PerlPooch/MQTT-Agent/MQTT-Agent-Hardware/Gerbers/V1/MQTT Relay-F_Cu.pdf

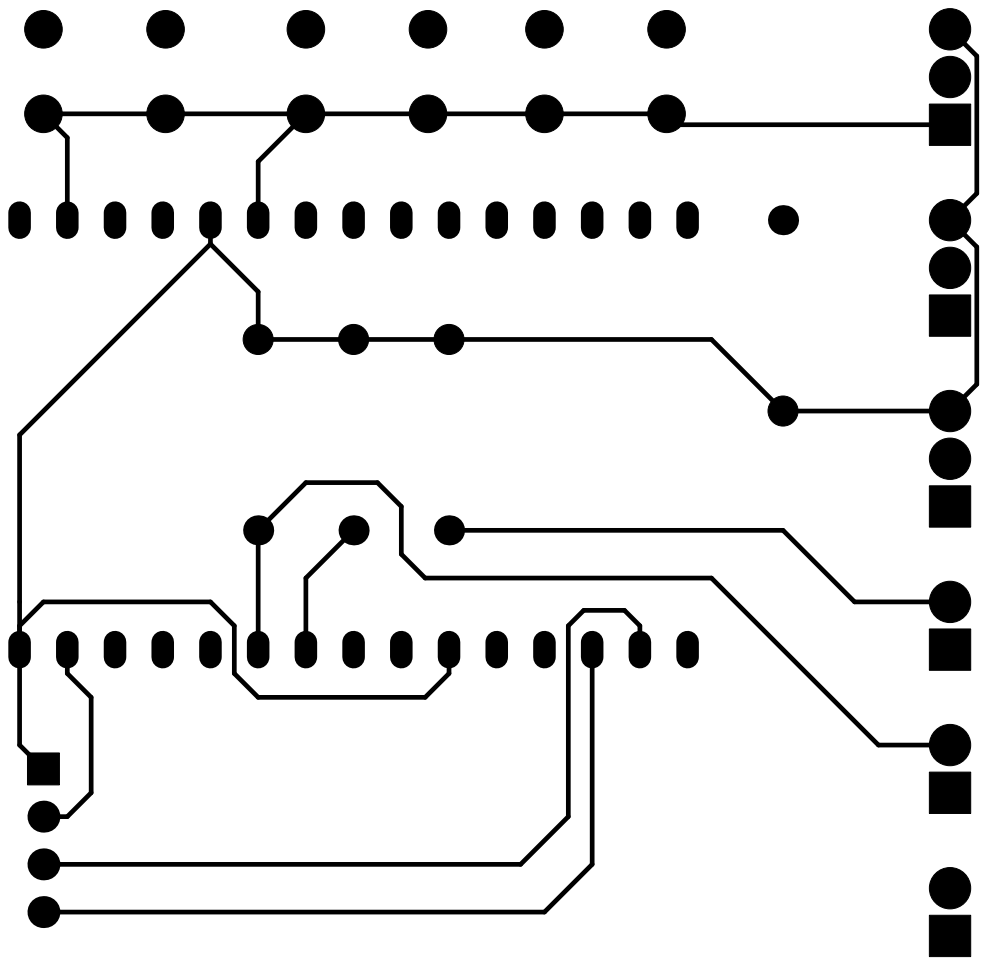
[picture p24: page 1]
