PerlPooch/MQTT-Agent/MQTT-Agent-Hardware/Gerbers/V1/MQTT Relay-F_SilkS.pdf

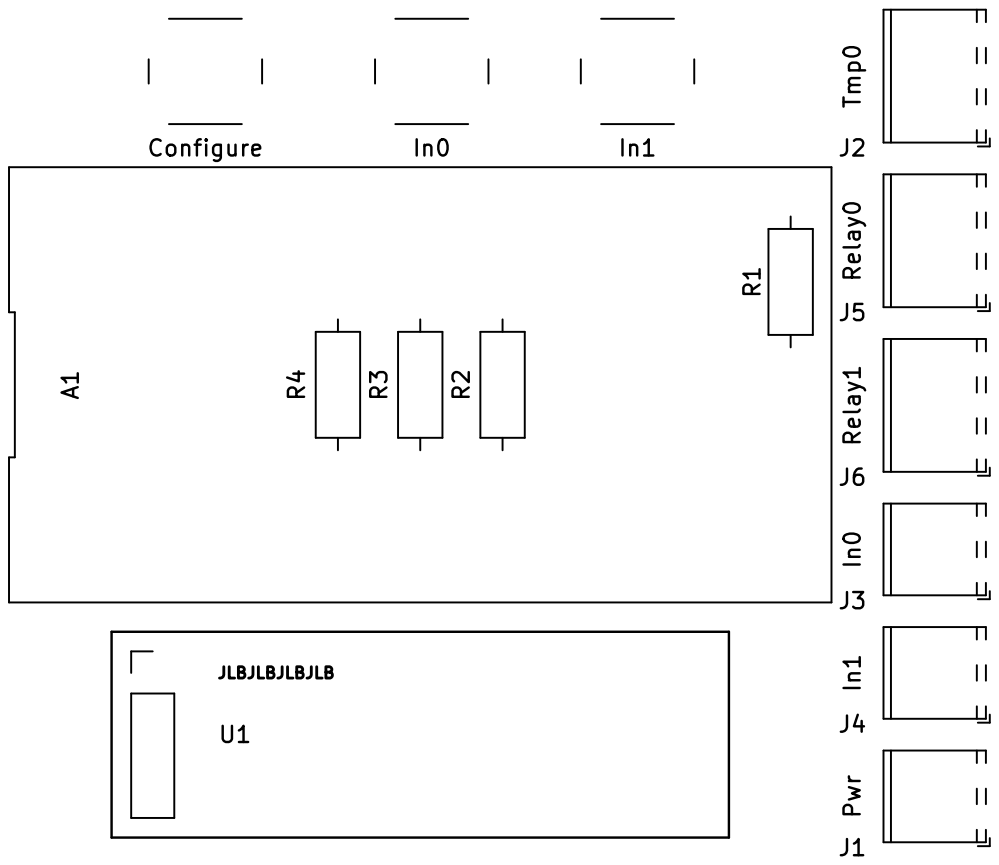
[picture p25: page 1]
