PerlPooch/MQTT-Agent/MQTT-Agent-Hardware/Gerbers/V1/MQTT Relay.pdf

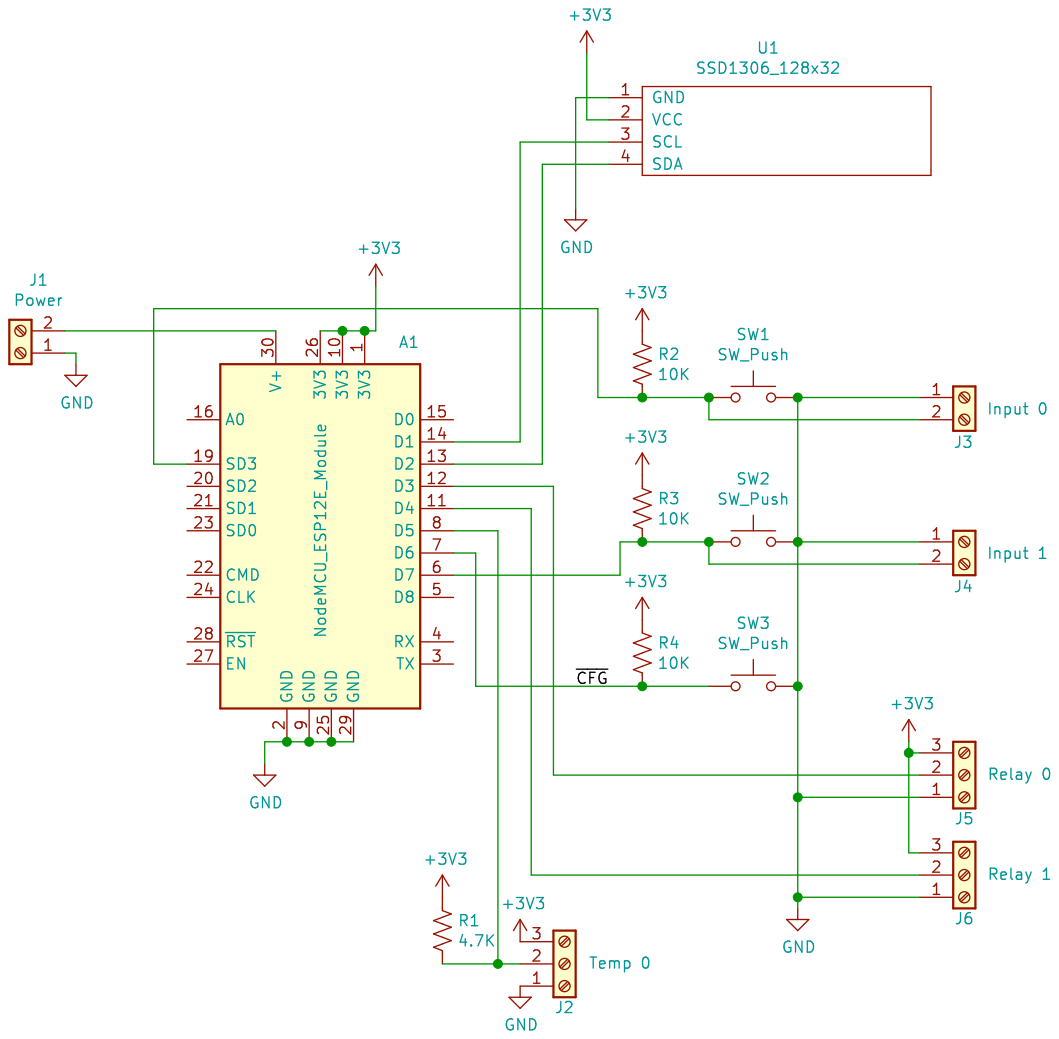
[picture p26: page 1]
